Ramprasad69975/ASIZSC-Converter-Design/PCB Images/Gerber 3D view.png

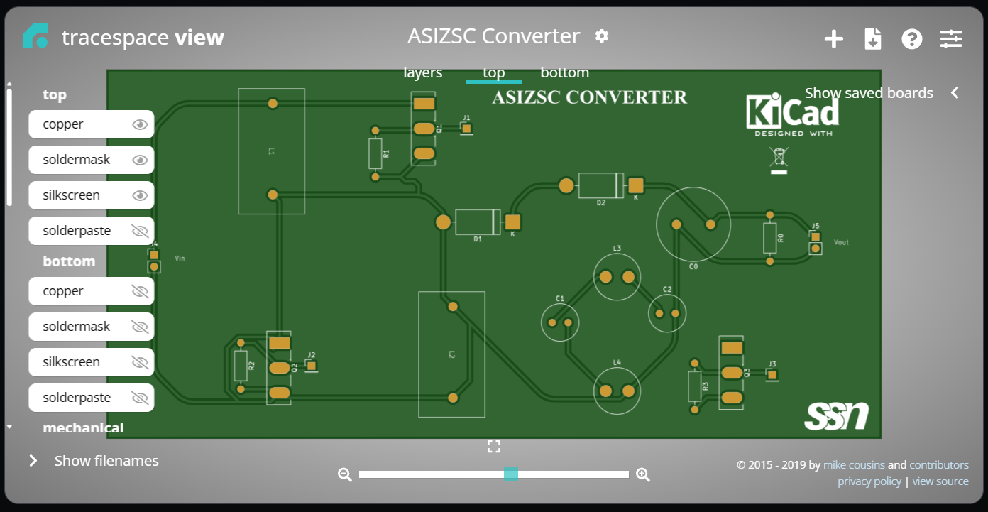
PCB Images/Gerber 3D view.png
