Ramprasad69975/ASIZSC-Converter-Design/PCB Images/Gerber file.png

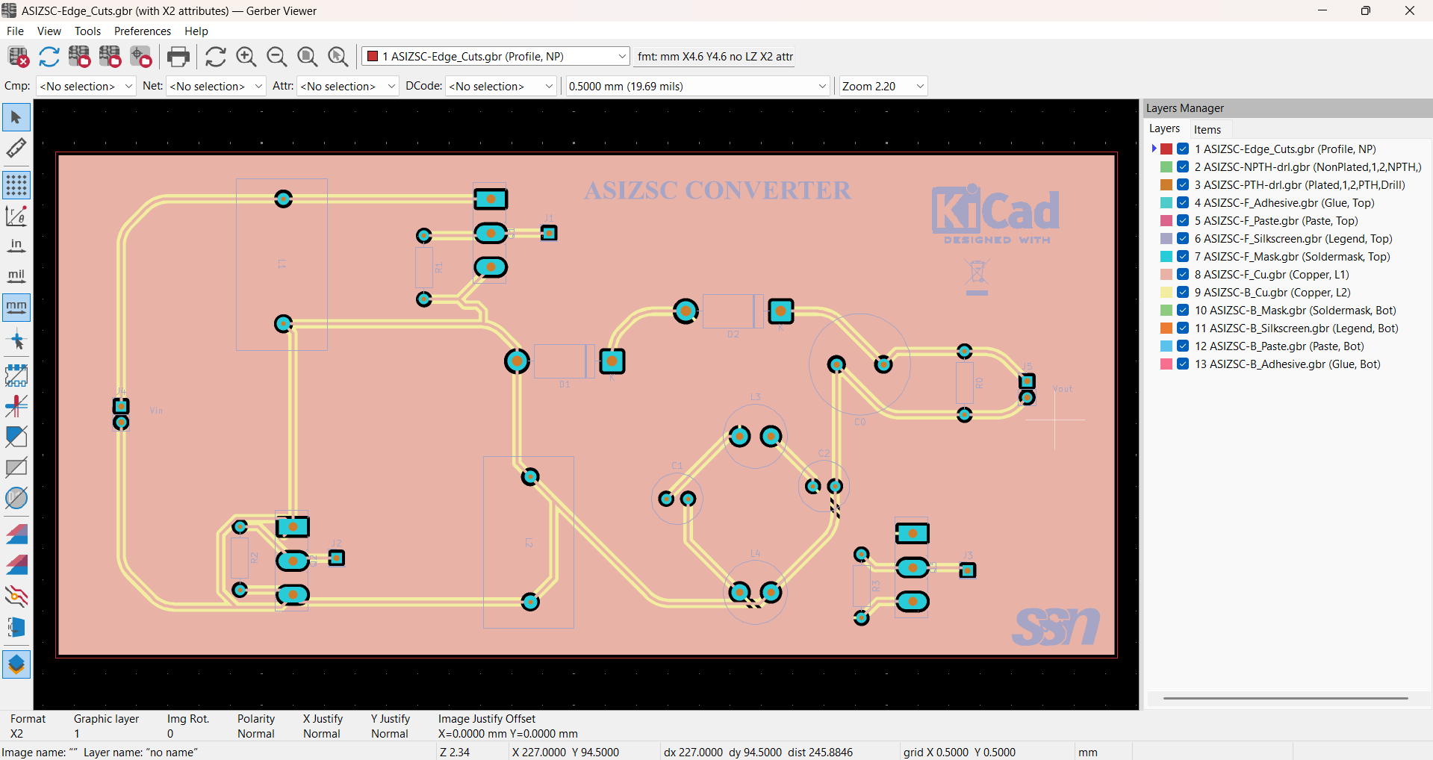
PCB Images/Gerber file.png
